CreatorsCollective/Creators-Collective_Mask-Straps/Fotos/20200508_095355.jpg

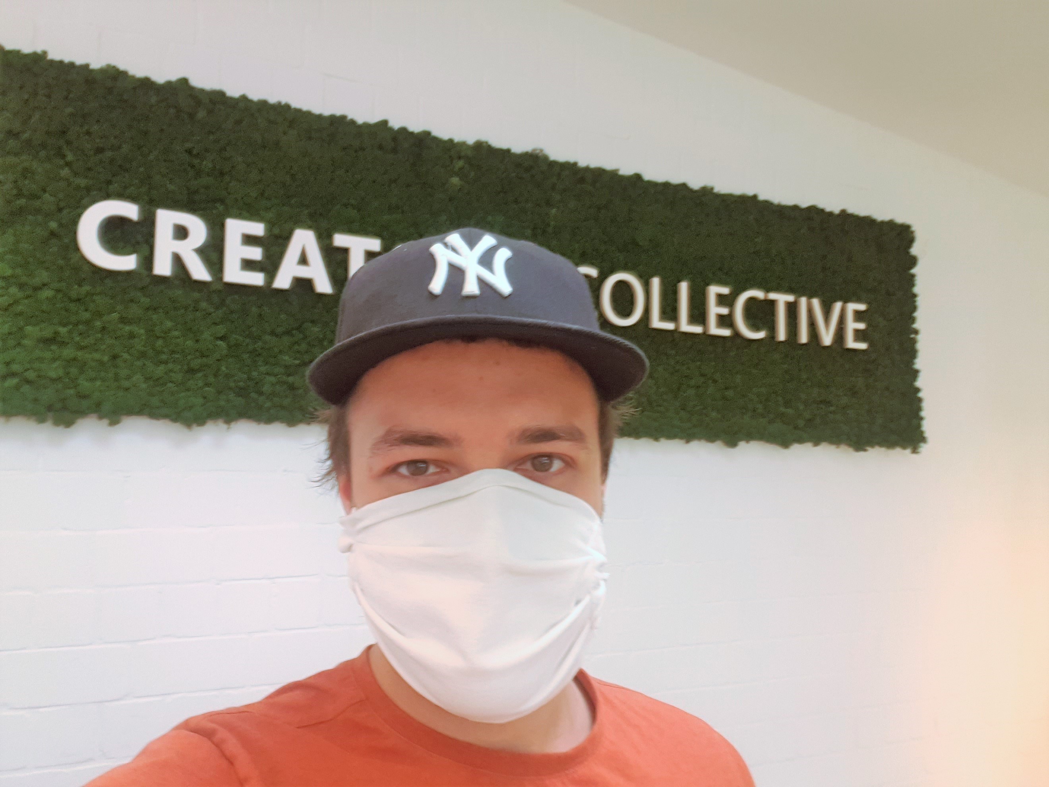
Fotos/20200508_095355.jpg
